jakiss/Radmesser/Auswertung_2020_09/Auswertung_anhand_Parameter/bei_40_1_kmh.JPG

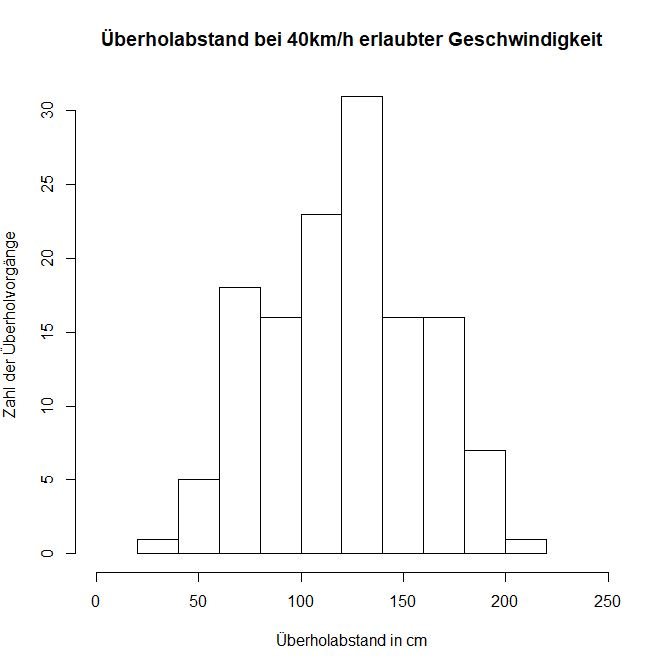
Auswertung_2020_09/Auswertung_anhand_Parameter/bei_40_1_kmh.JPG
