jakiss/Radmesser/Auswertung_2020_09/Auswertung_anhand_Parameter/Gesamtüberblick.JPG

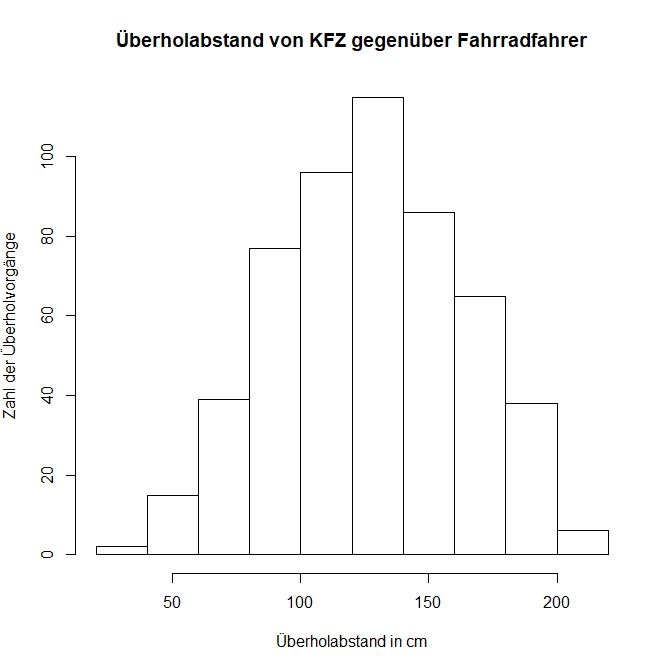
Auswertung_2020_09/Auswertung_anhand_Parameter/Gesamtüberblick.JPG
