jakiss/Radmesser/Auswertung_2020_09/Auswertung_anhand_Parameter/Gesamtüberblick_1.JPG

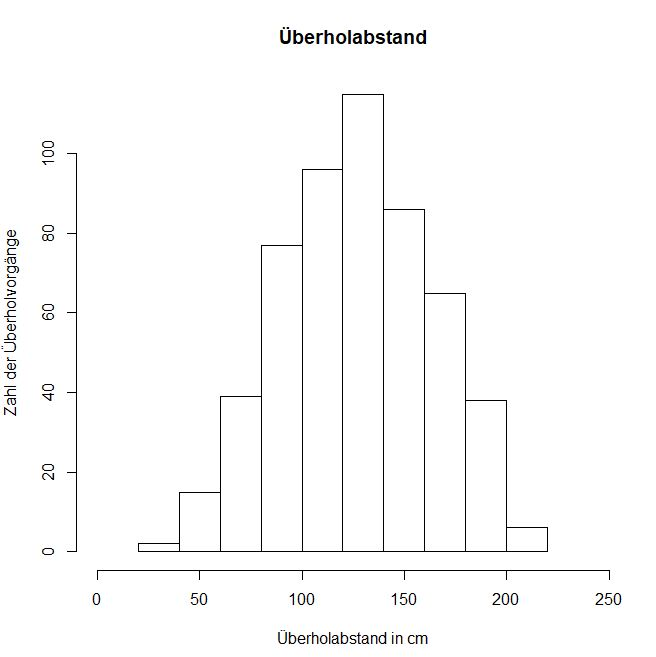
Auswertung_2020_09/Auswertung_anhand_Parameter/Gesamtüberblick_1.JPG
