jakiss/Radmesser/Auswertung_2020_09/Auswertung_anhand_Parameter/Strassen/1_primary.JPG

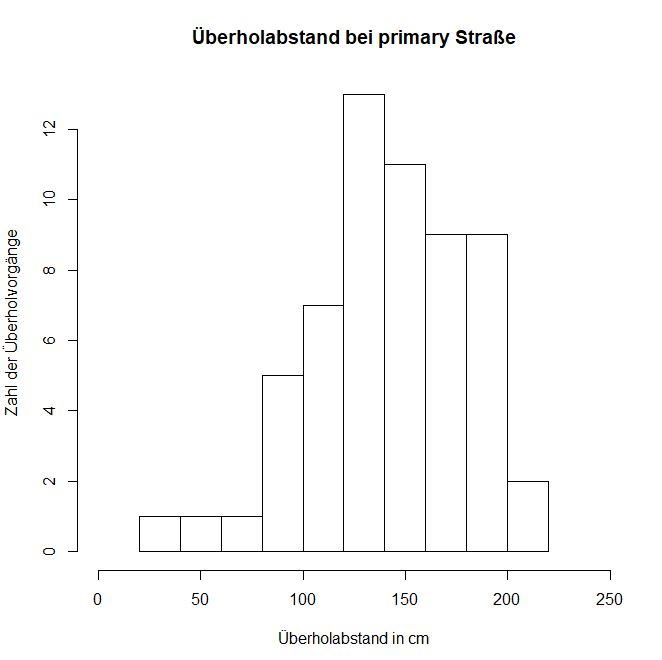
Auswertung_2020_09/Auswertung_anhand_Parameter/Strassen/1_primary.JPG
