jakiss/Radmesser/Auswertung_2020_09/Auswertung_anhand_Parameter/Strassen/3_tertiary.JPG

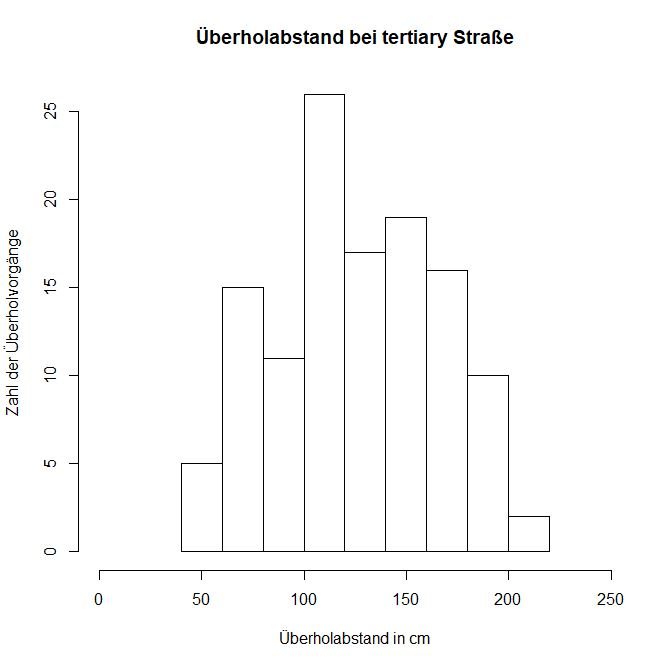
Auswertung_2020_09/Auswertung_anhand_Parameter/Strassen/3_tertiary.JPG
