jakiss/Radmesser/Auswertung_2020_09/Auswertung_anhand_Parameter/Strassen/5_track.JPG

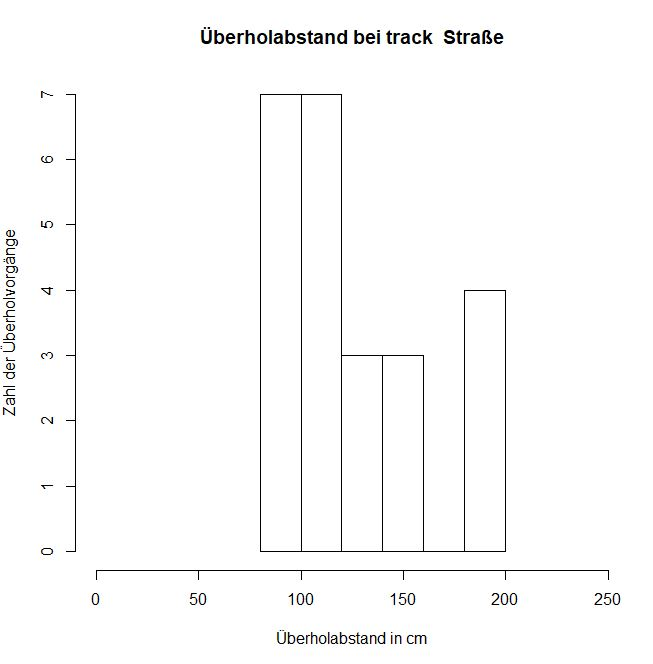
Auswertung_2020_09/Auswertung_anhand_Parameter/Strassen/5_track.JPG
