jakiss/Radmesser/Auswertung_2020_09/Auswertung_anhand_Parameter/Strassen/Boeblinger_Str_126.8cm.JPG

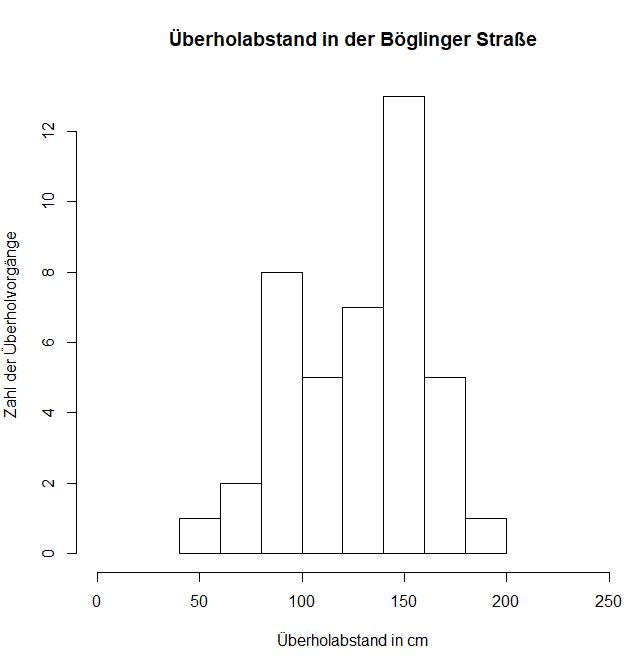
Auswertung_2020_09/Auswertung_anhand_Parameter/Strassen/Boeblinger_Str_126.8cm.JPG
