jakiss/Radmesser/Auswertung_2020_09/Auswertung_anhand_Parameter/Strassen/Rotebuehlstr_103.8cm.JPG

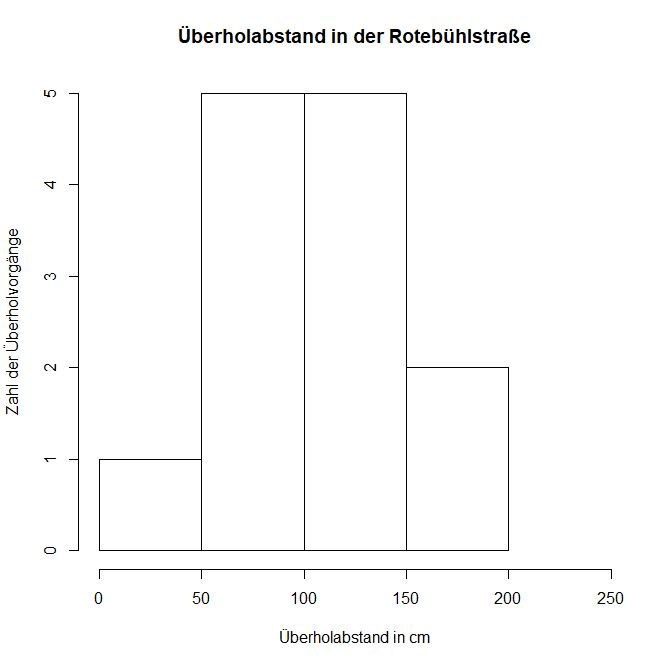
Auswertung_2020_09/Auswertung_anhand_Parameter/Strassen/Rotebuehlstr_103.8cm.JPG
