jakiss/Radmesser/Auswertung_2020_09/Auswertung_anhand_Parameter/Strassen/Silberburgstr_115.1cm.JPG

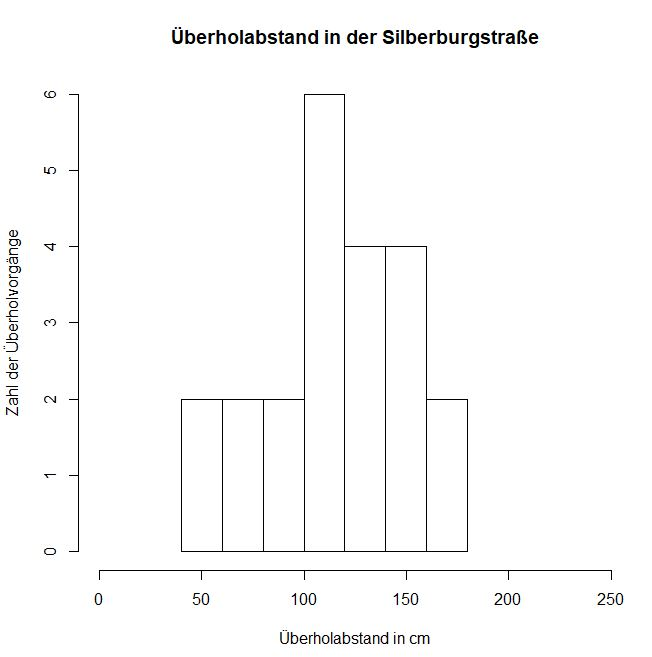
Auswertung_2020_09/Auswertung_anhand_Parameter/Strassen/Silberburgstr_115.1cm.JPG
