jakiss/Radmesser/Auswertung_2020_09/Auswertung_anhand_Parameter/Strassen/Theodor_Heuss_Str_127.5cm.JPG

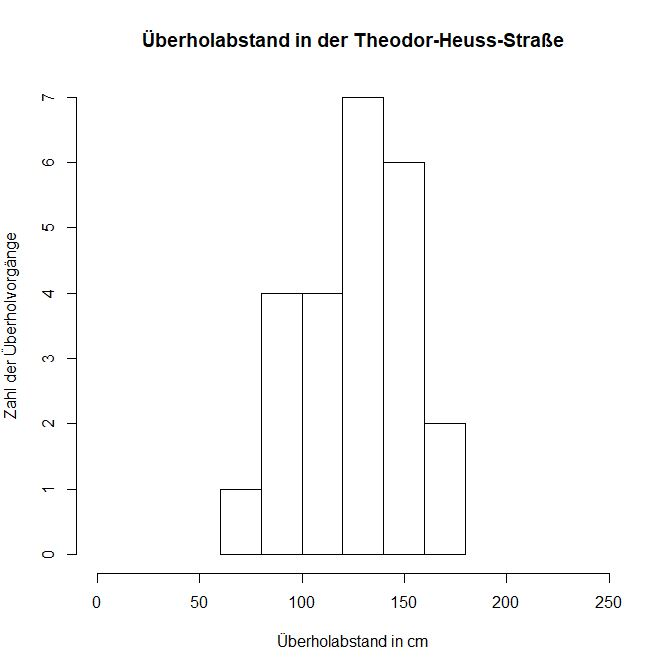
Auswertung_2020_09/Auswertung_anhand_Parameter/Strassen/Theodor_Heuss_Str_127.5cm.JPG
