jakiss/Radmesser/Anleitung_v01_20201018/Bilder/20200725_171343(2).jpg

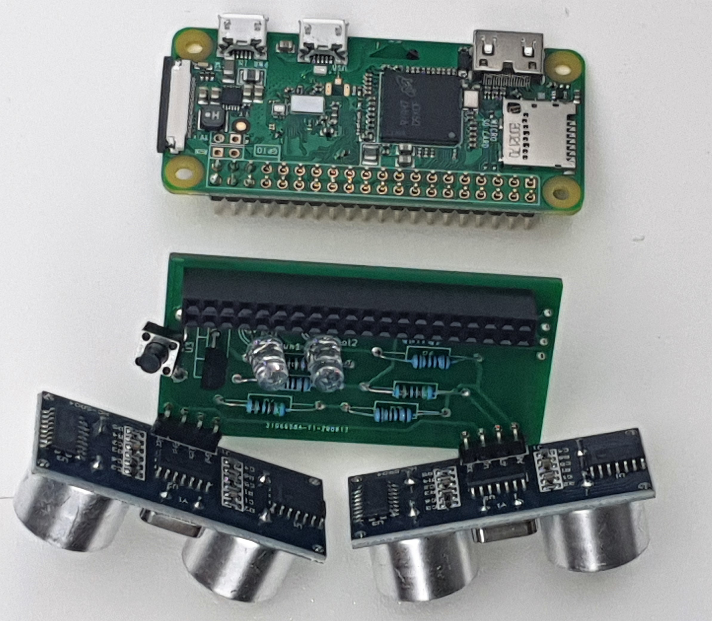
Anleitung_v01_20201018/Bilder/20200725_171343(2).jpg
